sparkfunX/Qwiic_Relay/Software/Example2-ChangeAddress/Example2-ChangeAddress.ino

/******************************************************************************
  Qwiic Joystiic Example 2 - Change Slave Address
  Kevin Kuwata @ SparkX
  March 21, 2018
  https://github.com/sparkfunX/Qwiic_Relay
  Arduino 1.8.5

  This sketch demonstrates how to change the Slave Addres
  of the Qwiic Relay. The new address will be saved to the
  Relay's EEPROM.

  The factory default slave address is 0x18.


******************************************************************************/
#include <Wire.h>

byte LATEST_ADDRESS = 0x18;     //Default Address

void setup() {
  Serial.begin(9600);
  Serial.println("Qwiic Relay Master Awake");
  Wire.begin(); // join the I2C Bus

  Wire.beginTransmission(LATEST_ADDRESS); // transmit to device
  //check here for an ACK from the slave
  //if Wire.endTransmission() returns a 2, slave not found.
  if (Wire.endTransmission() == 2) {
    Serial.println("Check Connections. Slave not found.");
  }
  else {
    Serial.println("Qwiic Relay found!");
  }
}

void loop() {
  relayOn(); // Turn on the Relay
  delay(1000);
  changeAddress(0x19); // Change the Relay's address to 0x19
  delay(100);   //Allow the slave time to change it's address.
  relayOff(); // Turn off the Relay
  delay(1000);

  changeAddress(0x00); // Try to change address to Invalid Address.
  delay(1000);
}


// changeAddress() takes a 7 bit I2C Address
// and writes it to the Relay. This function
// checks to see if the address is between
// 0x07 and 0x78. If valid, the new address is
// saved to the Relay's EEPROM. If not valid
// address is not changed.
// This function returns 0 if succesful and
// -1 if unsuccessful.
int changeAddress(byte _address) {
//check here for an ACK from the slave
    //if Wire.endTransmission() returns a 2, Slave not found.
    if (Wire.endTransmission() == 2) {
      Serial.println("Check Connections. No slave found.");
      return -1;
    }
    else {
      Wire.beginTransmission(LATEST_ADDRESS);
    }


  
  //check if valid address.
  if (_address > 0x07 && _address < 0x78) {
    Serial.print("The current address is: ");
    Serial.println(LATEST_ADDRESS, HEX);

    //valid address
    Wire.beginTransmission(LATEST_ADDRESS); // transmit to device

    Wire.write(0x03);        // writes the change address command
    LATEST_ADDRESS = _address;
    Wire.write(LATEST_ADDRESS);              // sends new address
    Wire.endTransmission();    // stop transmitting
    Wire.begin(LATEST_ADDRESS);// start with the new address..
    Serial.print("The new address is: 0x");
    Serial.println(_address, HEX);
  }
  else {
    Serial.print("The address 0x");
    Serial.print(_address);
    Serial.println(" is a valid I2C Address. Needs to be between 0x77 and 0x78.");
    Serial.print("The address is still: 0x");
    Serial.println(LATEST_ADDRESS, HEX);
    return -1;
  }
  return 0;
}




// RelayOn() turns on the relay at the SLAVE_ADDRESS
// Checks to see if a slave is connected and prints a
// message to the Serial Monitor if no slave found.
void relayOn() {
  Wire.beginTransmission(LATEST_ADDRESS); // transmit to default address: 0x18
  // Check for an ACK from the slave
  // If Wire.endTransmission() returns 2, No slave was found.

  if (Wire.endTransmission() == 2) {
    Serial.println("Check Connections. Slave not found.");
  }
  else {
    Wire.beginTransmission(LATEST_ADDRESS); // transmit to device 0x18
    Wire.write(0x01);           // Writes 0x01 to the Slave
    Wire.endTransmission();     // stop transmitting
    Serial.println("Relay is on.");
  }
}


// RelayOff() turns off the relay at the SLAVE_ADDRESS
// Checks to see if a slave is connected and prints a
// message to the Serial Monitor if no slave found.
void relayOff() {
  Wire.beginTransmission(LATEST_ADDRESS); // transmit to device 0x18
  // Check for an ACK from the slave
  // If Wire.endTransmission() returns 2, No slave was found.
  if (Wire.endTransmission() == 2) {
    Serial.println("Check Connections. Slave not found.");
  }
  else {
    Wire.beginTransmission(LATEST_ADDRESS); // transmit to device 0x18
    Wire.write(0x00);              // Writes 0x00 to the Slave
    Wire.endTransmission();       // stop transmitting
    Serial.println("Relay is off.");
  }
}
